nomurshin/ARViS_Automated_Robotic_Virus_injection_System/Data/Final_model_dataset/test/images/192_test.tif

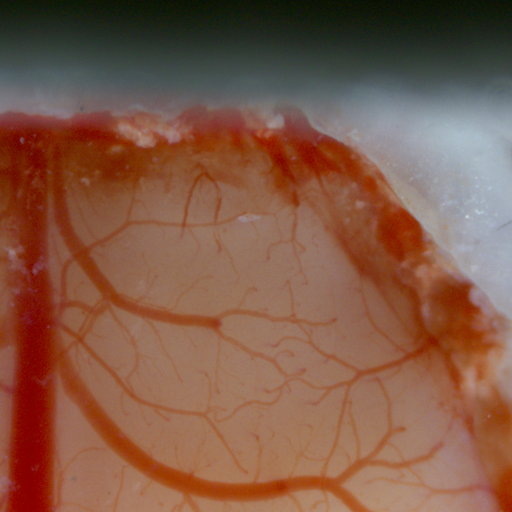
Data/Final_model_dataset/test/images/192_test.tif
