nomurshin/ARViS_Automated_Robotic_Virus_injection_System/Data/demo/masks/standard17.png

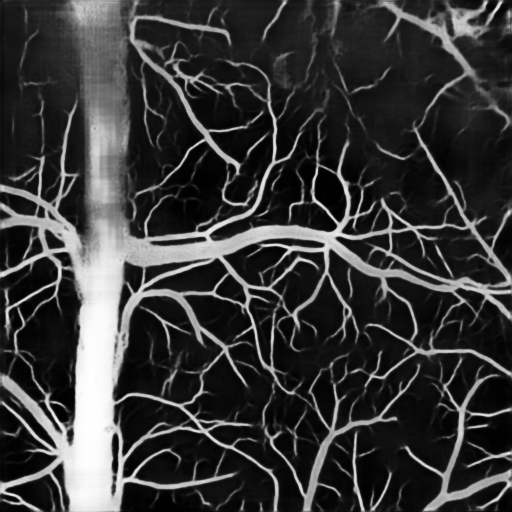
Data/demo/masks/standard17.png
