nomurshin/ARViS_Automated_Robotic_Virus_injection_System/Data/demo/masks/standard19.png

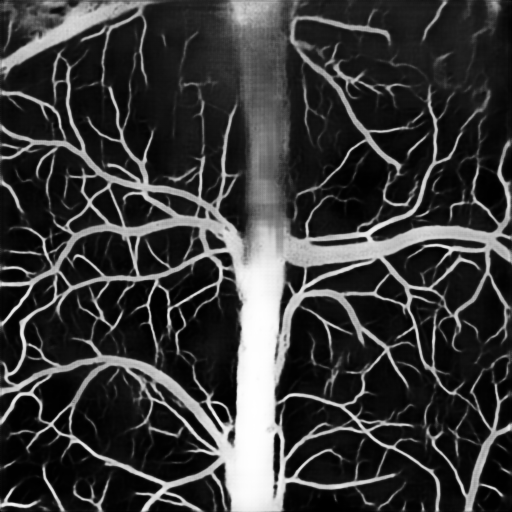
Data/demo/masks/standard19.png
