nomurshin/ARViS_Automated_Robotic_Virus_injection_System/Data/demo/masks/standard27.png

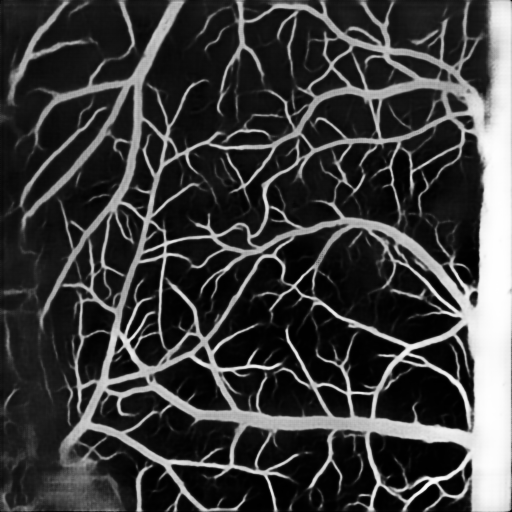
Data/demo/masks/standard27.png
