nomurshin/ARViS_Automated_Robotic_Virus_injection_System/Data/demo/pano.jpg

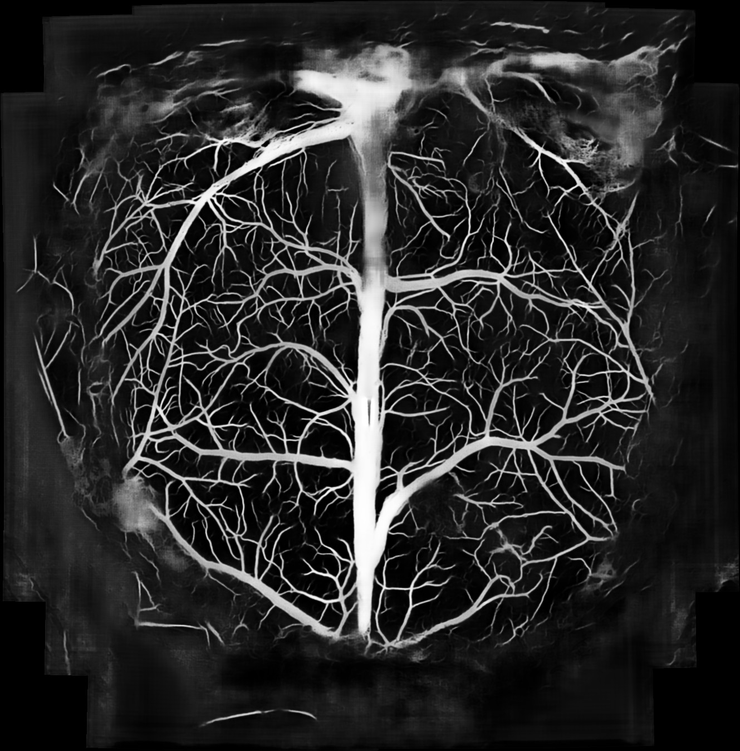
Data/demo/pano.jpg
