nomurshin/ARViS_Automated_Robotic_Virus_injection_System/Data/Final_model_dataset/training/images/129_training.png

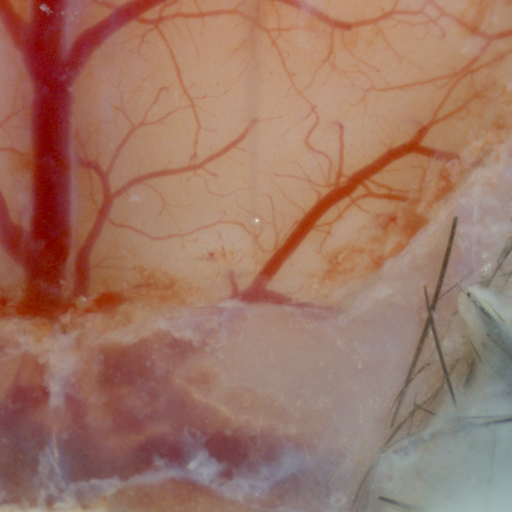
Data/Final_model_dataset/training/images/129_training.png
