nomurshin/ARViS_Automated_Robotic_Virus_injection_System/Data/Final_model_dataset/test/labels/192_manual1.PNG

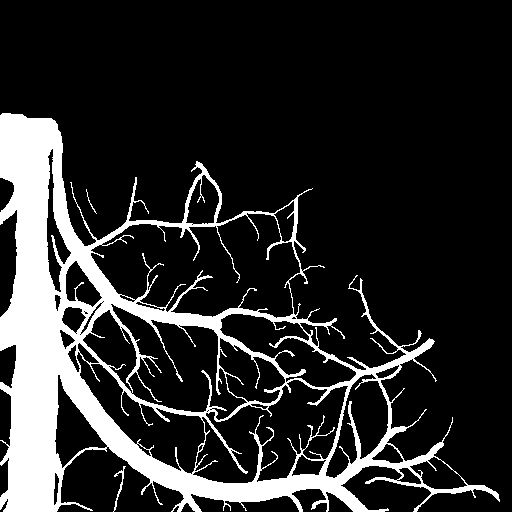
Data/Final_model_dataset/test/labels/192_manual1.PNG
