nomurshin/ARViS_Automated_Robotic_Virus_injection_System/Data/Final_model_dataset/test/labels/215_manual1.PNG

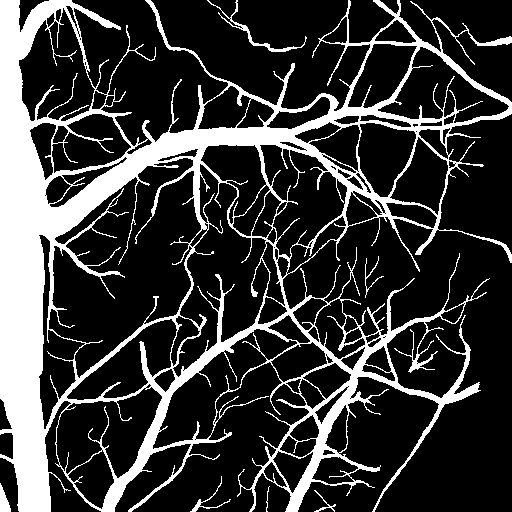
Data/Final_model_dataset/test/labels/215_manual1.PNG
