nomurshin/ARViS_Automated_Robotic_Virus_injection_System/Data/Final_model_dataset/training/labels/43_manual1.png

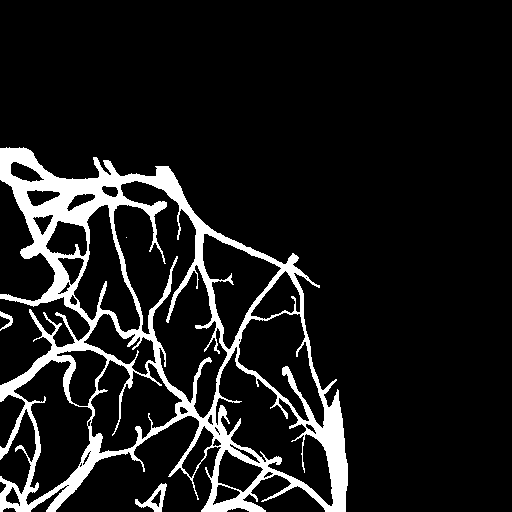
Data/Final_model_dataset/training/labels/43_manual1.png
